Tremendo97/HandTwin/stl/poleas/poleas_v13.stl

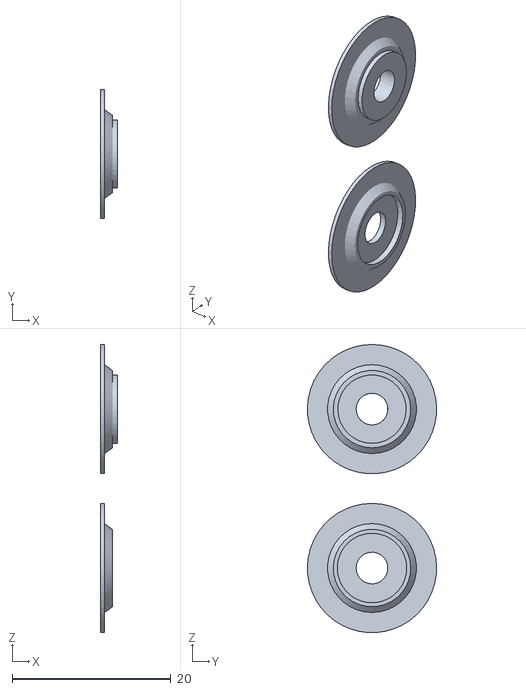
[picture p15: CAD file, 2026-06-09]
stl/poleas/poleas_v13.stl
2.10 x 16.3 x 36.2
