Tremendo97/HandTwin/stl/pulgar/falange3_Pulgar_v13.stl

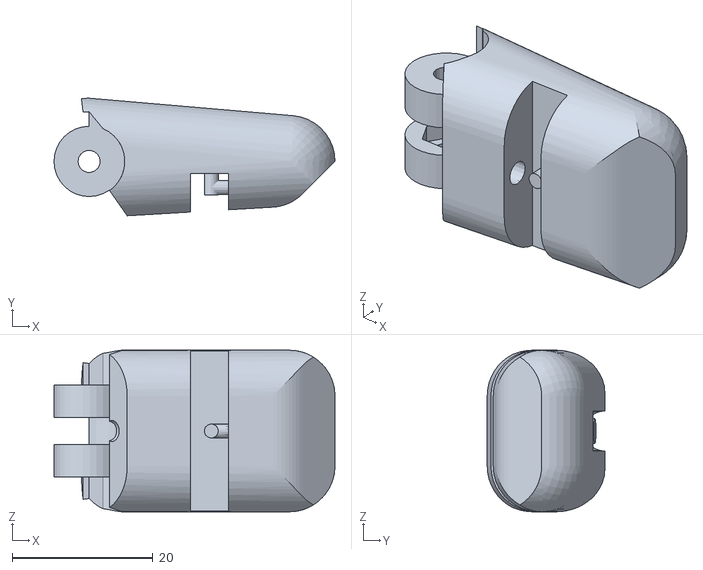
[picture p16: CAD file, 2026-06-09]
stl/pulgar/falange3_Pulgar_v13.stl
40.0 x 16.7 x 23.0
