Tremendo97/HandTwin/stl/sujeciones_dedos_V13.stl

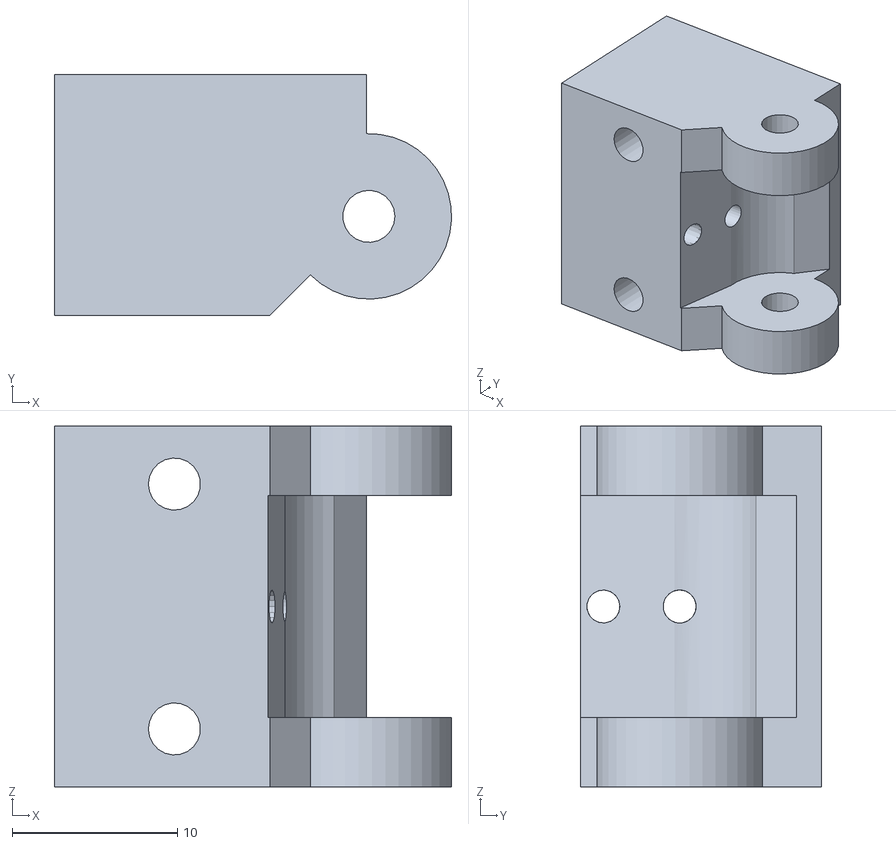
[picture p17: CAD file, 2026-06-09]
stl/sujeciones_dedos_V13.stl
24.0 x 14.6 x 21.8
