Tremendo97/HandTwin/stl/palma_v13.stl

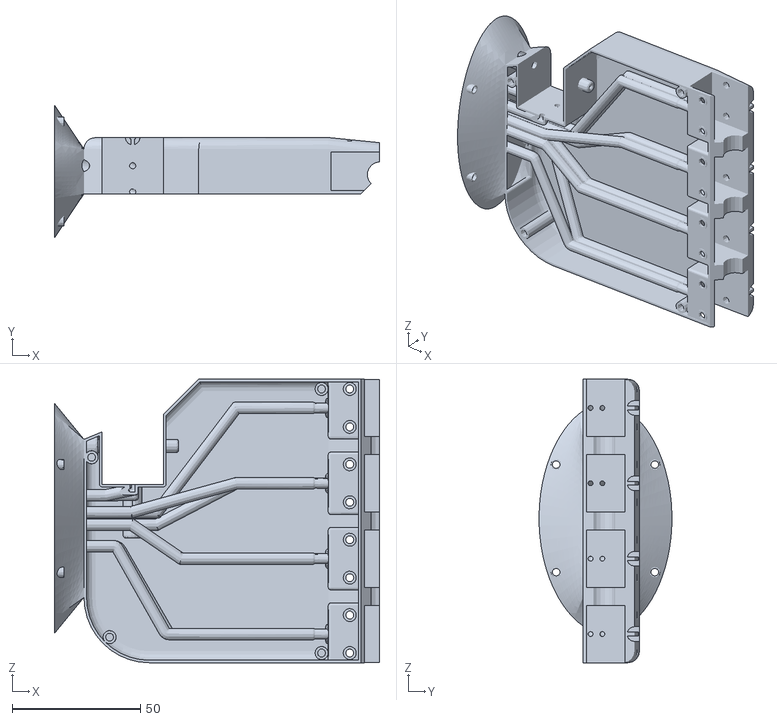
[picture p18: CAD file, 2026-06-09]
stl/palma_v13.stl
126.8 x 51.8 x 110.6
